maxvfischer/DIY-arcade/images/build/IMG_0449.JPG

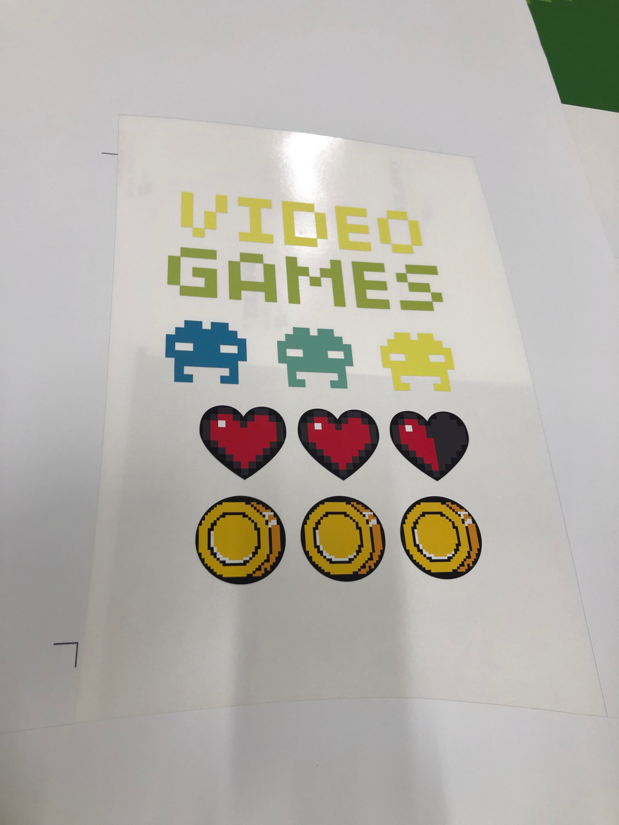
images/build/IMG_0449.JPG
