maxvfischer/DIY-arcade/images/build/light_box_18.jpg

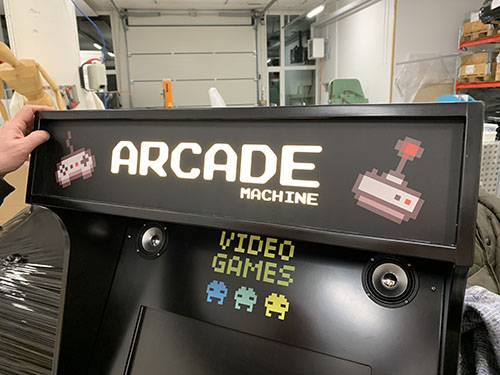
images/build/light_box_18.jpg
