maxvfischer/DIY-arcade/images/build/power_buttons_1.jpg

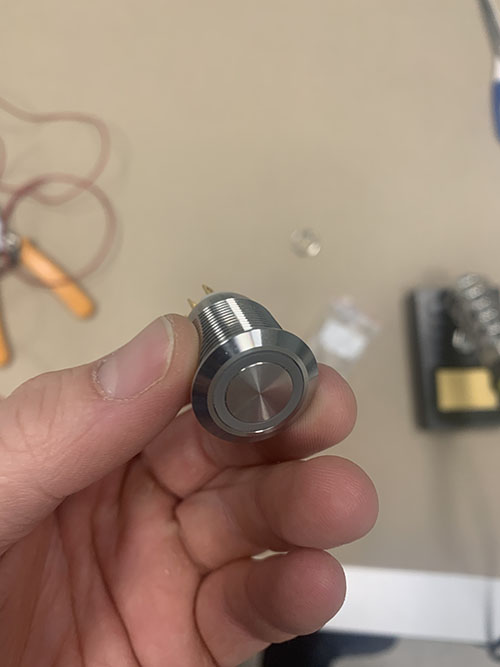
images/build/power_buttons_1.jpg
